lab11/atum/contiki/apps/adc_radio_test/app.h

#ifndef __APP_H__
#define __APP_H__

#include <stdint.h>

#define ADDR_ALL_ROUTERS "ff02::2"

#define RECEIVER_ADDR "2001:470:1f10:1320::2"
#define RECEIVER_PORT 4001
#define PROFILE_ID "G9T58vZ7Bi"

// Prefix for this node, just set it blank as we have no idea what the prefix
// will be.
#define IN6_PREFIX "::"

#define DATA_TYPE 0
#define VERSION 1

typedef struct {
  char     profile[10]; // GATD profile ID
  uint8_t  type;
  uint8_t  version;
  int16_t  airflow;
  uint32_t seq_no;
} __attribute__((packed)) pkt_data_t;

#endif


// 5): 0x3841c82b2200ffffae99f34f43e598c07c7010200104701f1013200000000000000002f051c70fa1df093761694f504a61705846017f2b
// 03877 got packet (78): 0x4f41c8932200ffff997d0f04004b120041600000000015110f0000000000000000c298e5434ff399ae200104701f101320000000000000000251c70fa10015df093761694f504a61705846017f2b
// 03878 got packet (78): 0x4f41c8942200ffff997d0f04004b120041600000000015110f0000000000000000c298e5434ff39e2d200104701f101320000000000000000251c70fa1001523cc3761694f504a61705846013de2
// 03879 got packet (55): 0x3841c84b2200ffffcb59f34f43e598c07c7010200104701f1013200000000000000002f051c70fa1ff383761694f504a6170584601334b
// 03880 got packet (78): 0x4f41c8952200ffff997d0f04004b120041600000000015110f0000000000000000c298e5434ff359cb200104701f101320000000000000000251c70fa10015ff383761694f504a6170584601334b
// 03881 got packet (55): 0x3841c8e92200ffff2057f34f43e598c07c7010200104701f1013200000000000000002f051c70fa163f43761694f504a617058460122e9
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
// 03898 got packet (78): 0x4f41c89f2200ffff997d0f04004b120041600000000015110f0000000000000000c298e5434ff33609200104701f101320000000000000000251c70fa1001502e93761694f504a6170584601456b
